ramonimbao/Alice-like_Handwired/firmware/config.h

/*
Copyright 2015 Jun Wako <wakojun@gmail.com>

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
You should have received a copy of the GNU General Public License
along with this program.  If not, see <http://www.gnu.org/licenses/>.
*/

#ifndef CONFIG_H
#define CONFIG_H

/* USB Device descriptor parameter */
#define VENDOR_ID       0xB16B
#define PRODUCT_ID      0x00B5
#define DEVICE_VER      0x0001
/* in python2: list(u"whatever".encode('utf-16-le')) */
/*   at most 32 characters or the ugly hack in usb_main.c borks */
#define MANUFACTURER Ramon Imbao
#define PRODUCT fAuxLICE
#define DESCRIPTION A handwired 3D-printed ergonomic keyboard

//#define PWM_AUDIO

#define MATRIX_ROW_PINS \
  { B11, B10, B1, B0, A7 }
#define MATRIX_COL_PINS \
  { B6, B7, B8, B9, C13, C14, C15, A0, A1, A2, A3, A4, A5, A6 }

/* key matrix size */
#define MATRIX_ROWS 5
#define MATRIX_COLS 14
#define DIODE_DIRECTION COL2ROW

/* define if matrix has ghost */
//#define MATRIX_HAS_GHOST

/* Set 0 if debouncing isn't needed */
#define DEBOUNCE    5

/* Mechanical locking support. Use KC_LCAP, KC_LNUM or KC_LSCR instead in keymap */
#define LOCKING_SUPPORT_ENABLE
/* Locking resynchronize hack */
#define LOCKING_RESYNC_ENABLE

/*
 * Feature disable options
 *  These options are also useful to firmware size reduction.
 */

/* disable debug print */
//#define NO_DEBUG

/* disable print */
//#define NO_PRINT

/* disable action features */
//#define NO_ACTION_LAYER
//#define NO_ACTION_TAPPING
//#define NO_ACTION_ONESHOT
//#define NO_ACTION_MACRO
//#define NO_ACTION_FUNCTION

#endif
